tropicsquare/devboards/TROPIC01_Arduino_Shield/TS1401/doc/Arduino_UNO_R3_Pinout.jpg

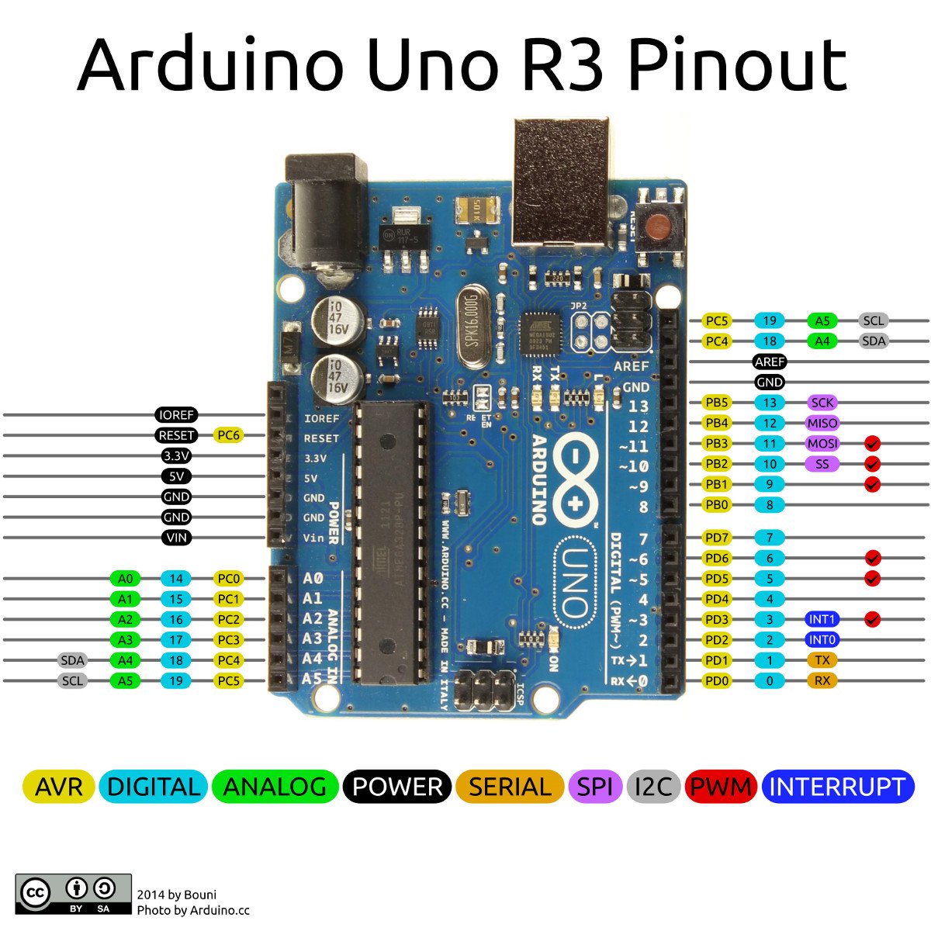
TROPIC01_Arduino_Shield/TS1401/doc/Arduino_UNO_R3_Pinout.jpg
