tropicsquare/devboards/TROPIC01_Arduino_Shield/TS1401/img/bot.png

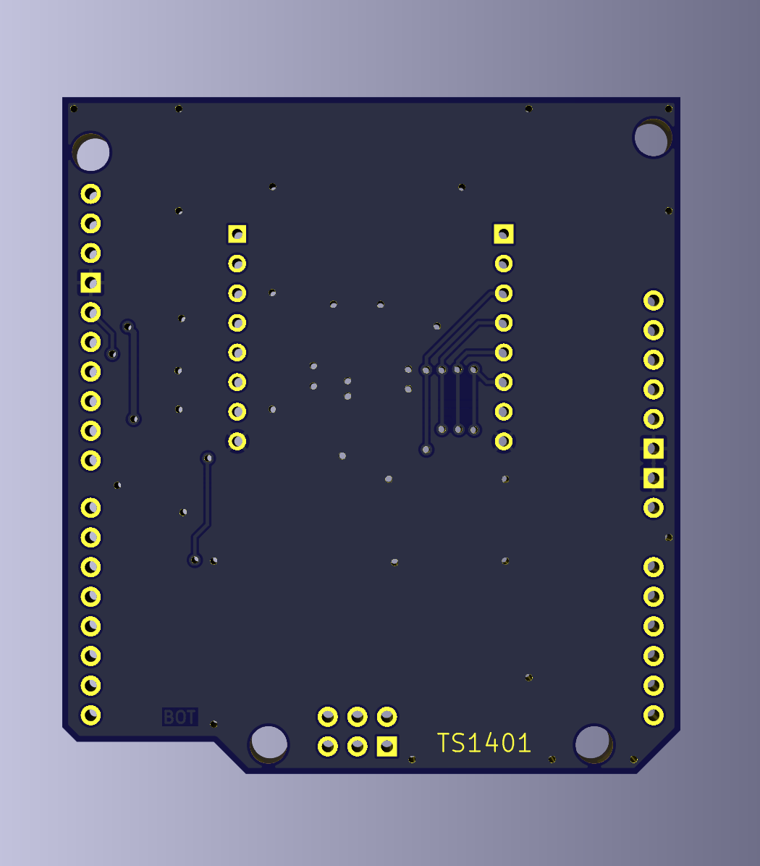
TROPIC01_Arduino_Shield/TS1401/img/bot.png
