tropicsquare/devboards/TROPIC01_Arduino_Shield/TS1401/img/top.png

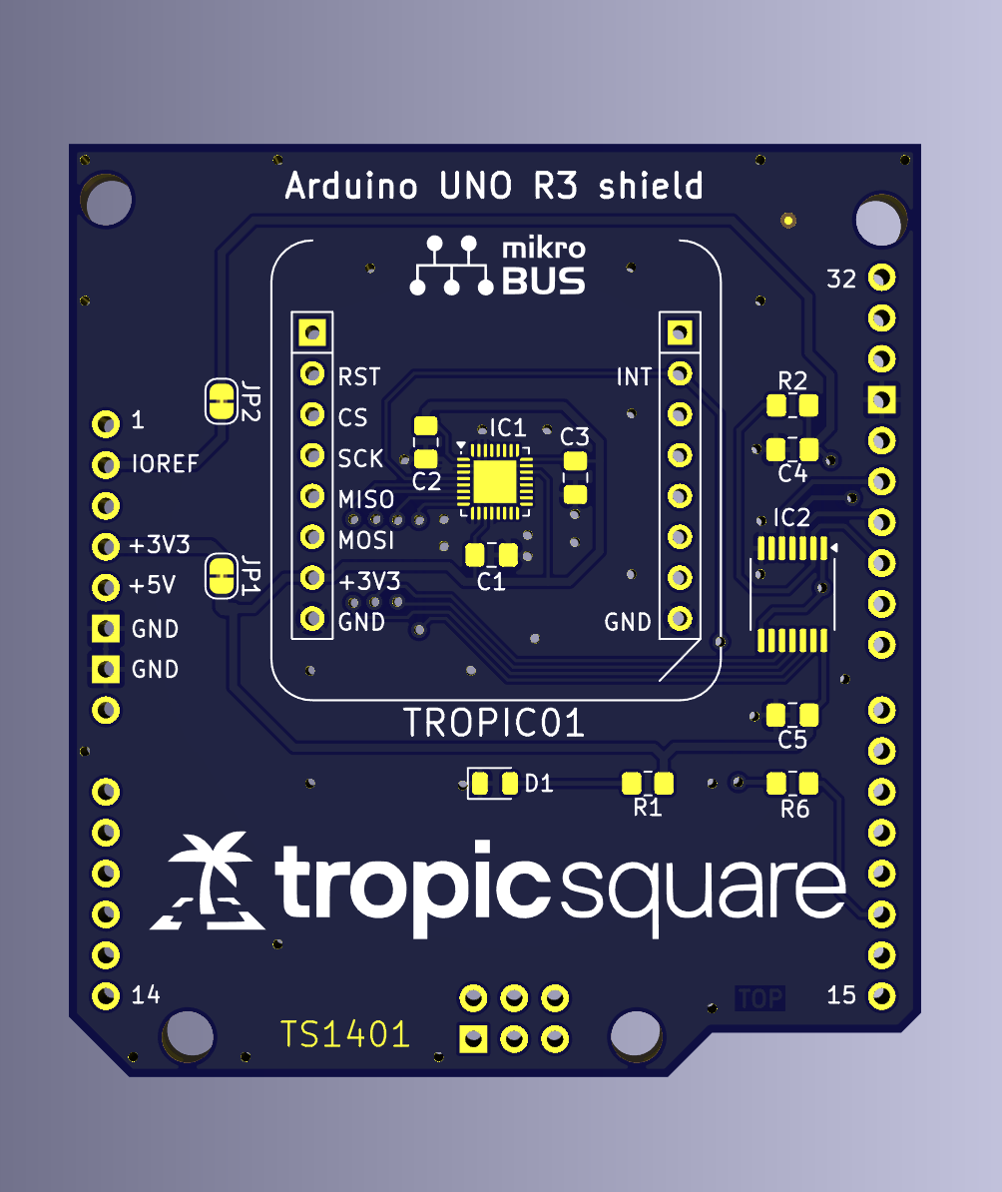
TROPIC01_Arduino_Shield/TS1401/img/top.png
