tropicsquare/devboards/TROPIC01_Mini_Board/TS1702/img/angle.png

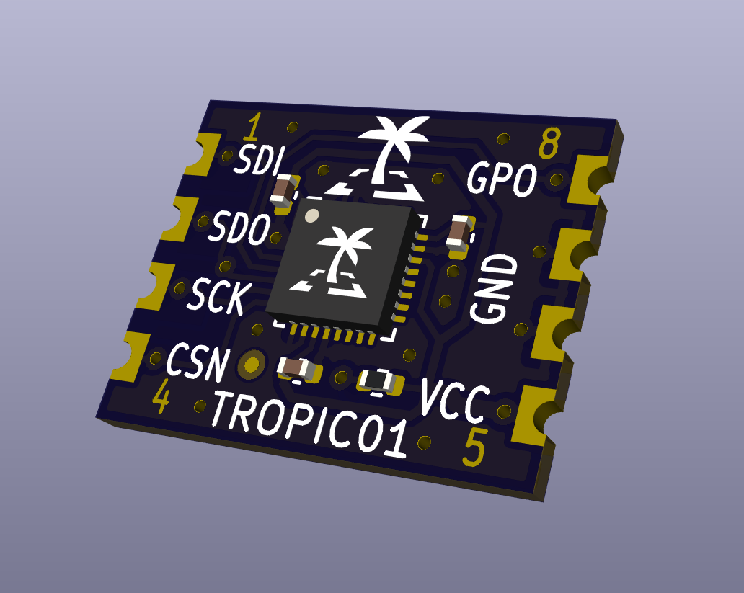
TROPIC01_Mini_Board/TS1702/img/angle.png
