tropicsquare/devboards/TROPIC01_Mini_Board/TS1702/img/bot.png

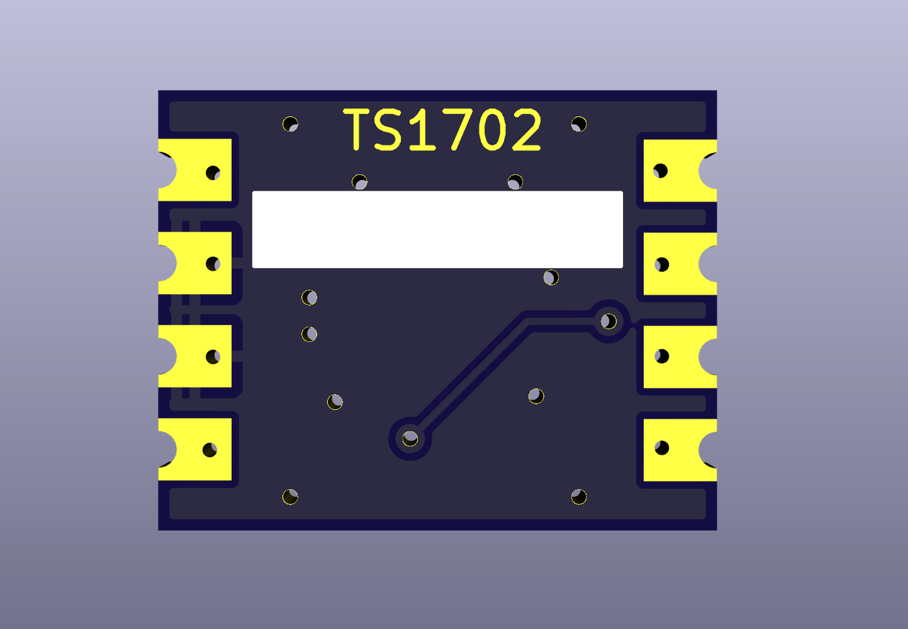
TROPIC01_Mini_Board/TS1702/img/bot.png
