tropicsquare/devboards/TROPIC01_Mini_Board/TS1702/img/dimensions.png

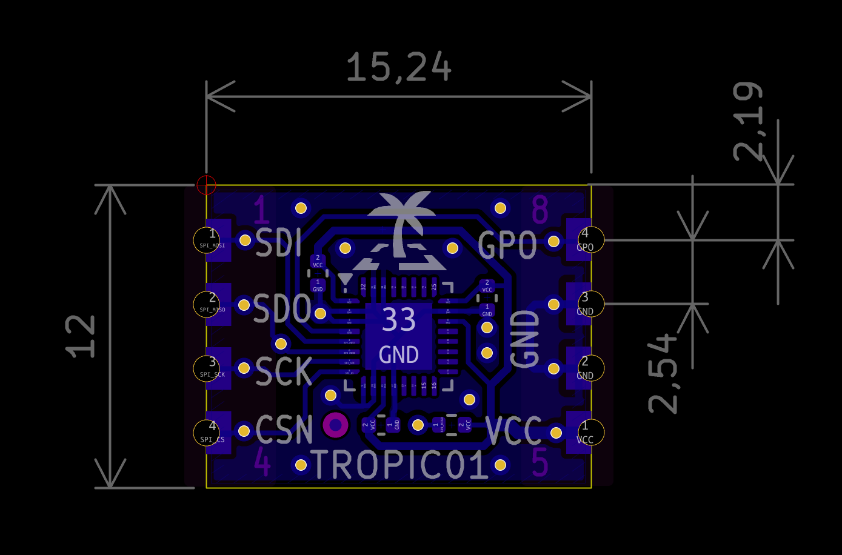
TROPIC01_Mini_Board/TS1702/img/dimensions.png
