tropicsquare/devboards/TROPIC01_Mini_Board/TS1702/img/overview.png

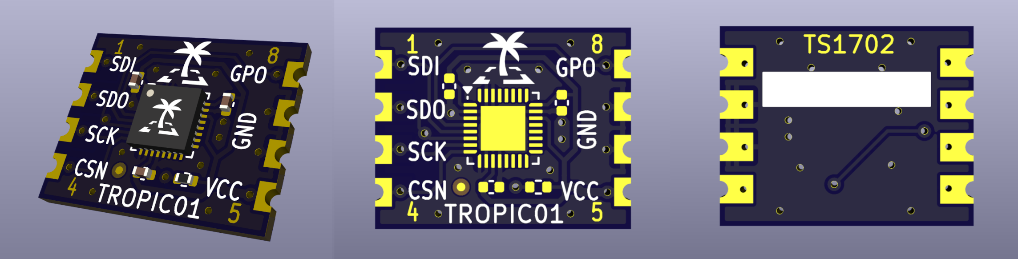
TROPIC01_Mini_Board/TS1702/img/overview.png
