tropicsquare/devboards/TROPIC01_Mini_Board/TS1702/img/top.png

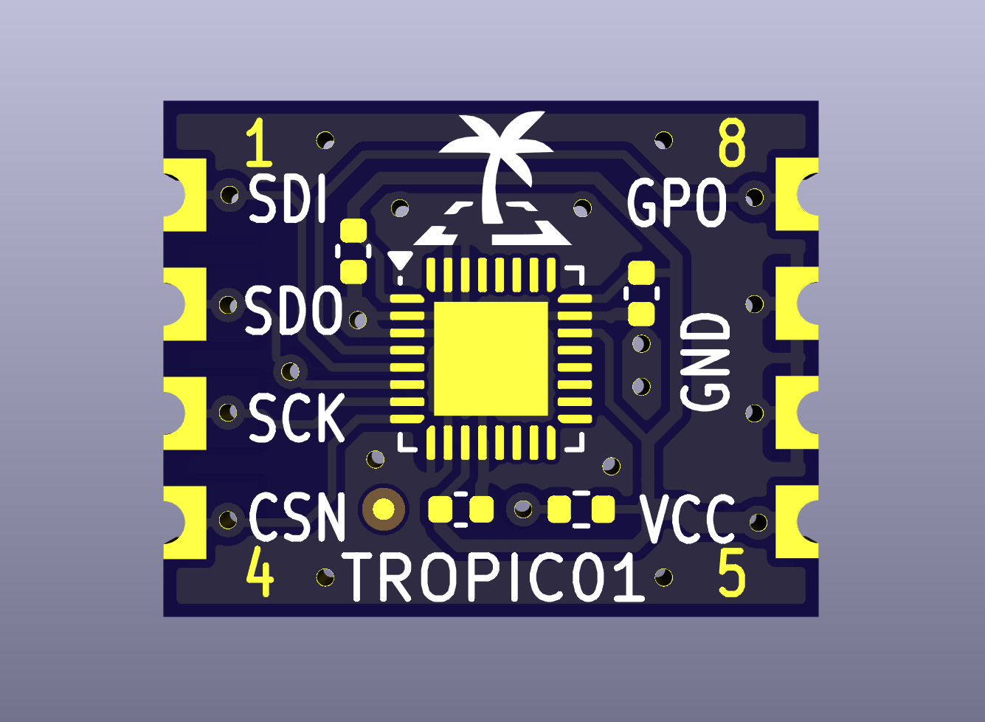
TROPIC01_Mini_Board/TS1702/img/top.png
