tropicsquare/devboards/TROPIC01_Raspberry_Pi_Shield/TS1501/img/top.png

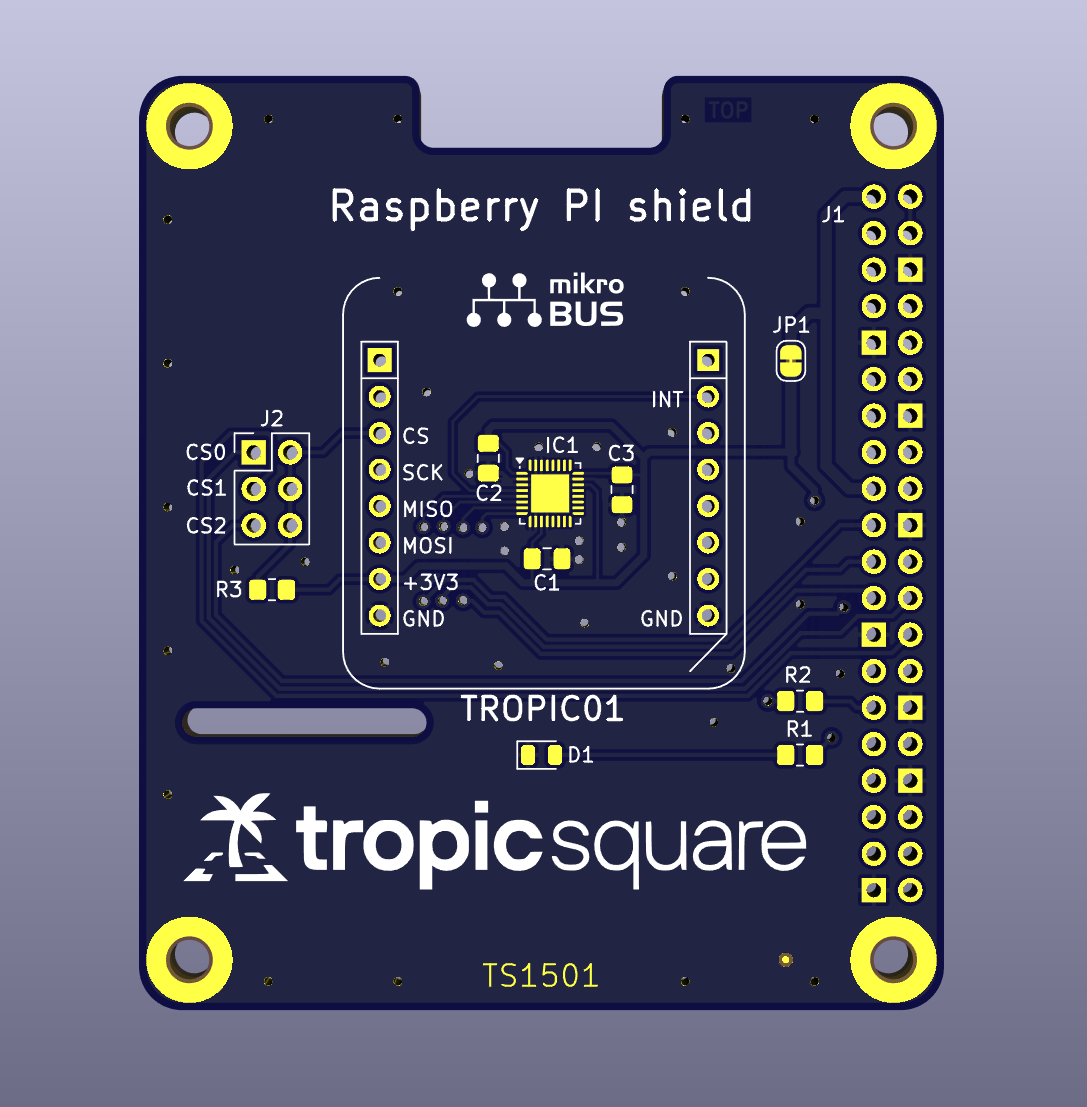
TROPIC01_Raspberry_Pi_Shield/TS1501/img/top.png
