tropicsquare/devboards/TROPIC01_USB_Devkit/firmwares/firmware_B/doc/ts1302_hw_bot.png

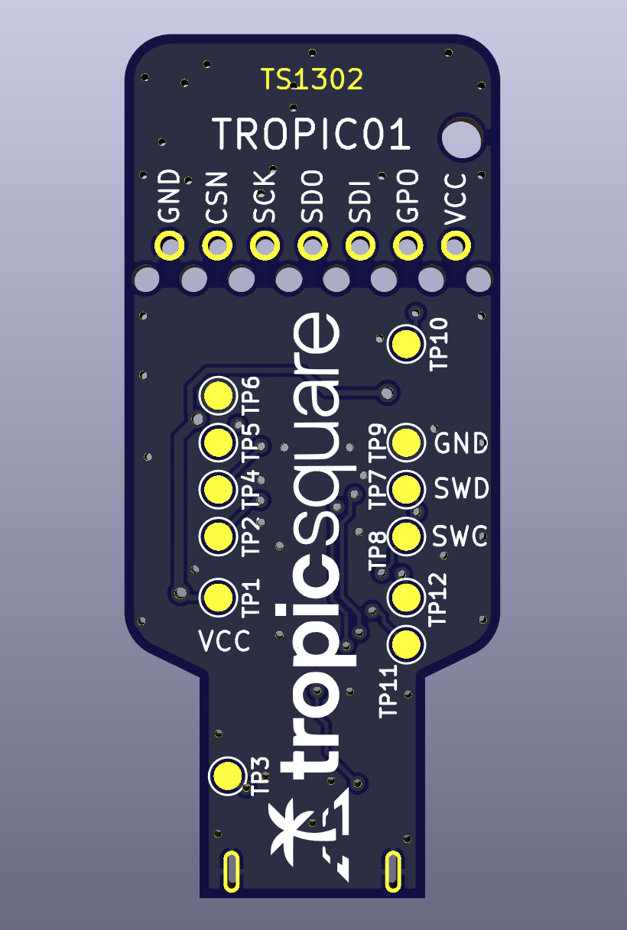
TROPIC01_USB_Devkit/firmwares/firmware_B/doc/ts1302_hw_bot.png
