tropicsquare/devboards/TROPIC01_USB_Devkit/firmwares/firmware_B/doc/ts1302_hw_top.png

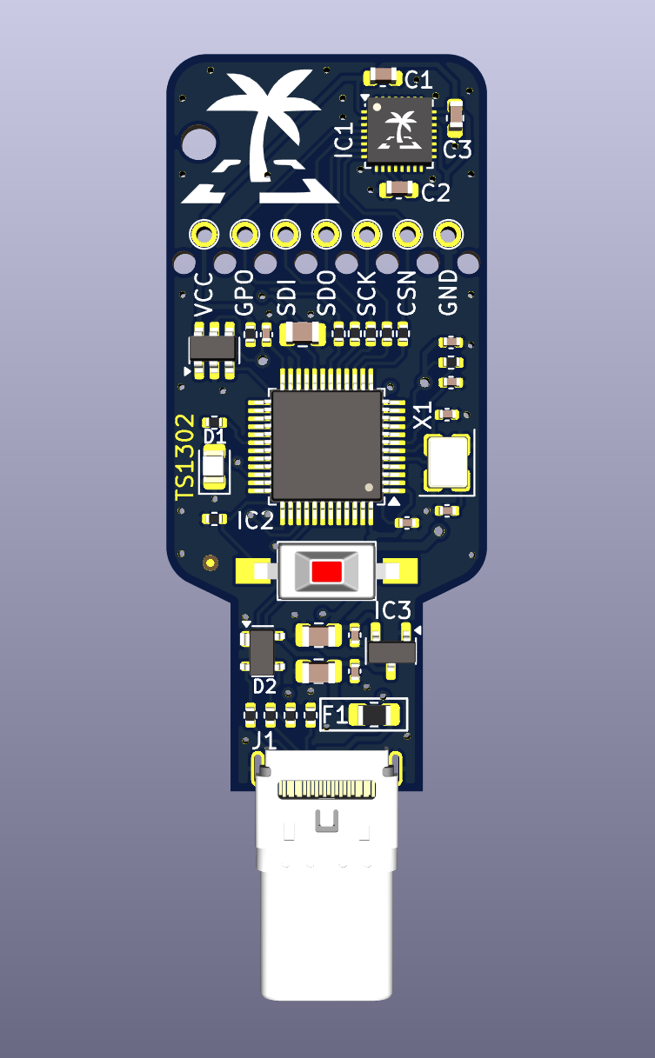
TROPIC01_USB_Devkit/firmwares/firmware_B/doc/ts1302_hw_top.png
