tropicsquare/devboards/TROPIC01_Arduino_Shield/TS1401/img/top_assembled.png

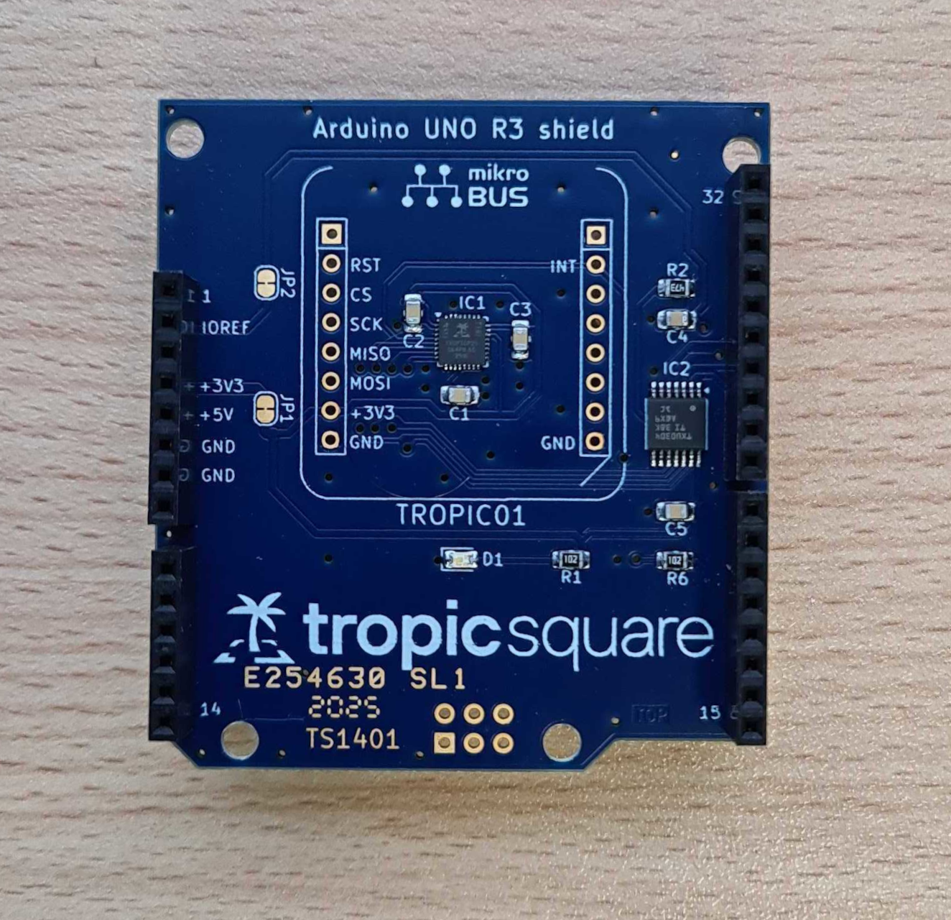
TROPIC01_Arduino_Shield/TS1401/img/top_assembled.png
