tropicsquare/devboards/TROPIC01_Raspberry_Pi_Shield/TS1501/img/bot_assembled.png

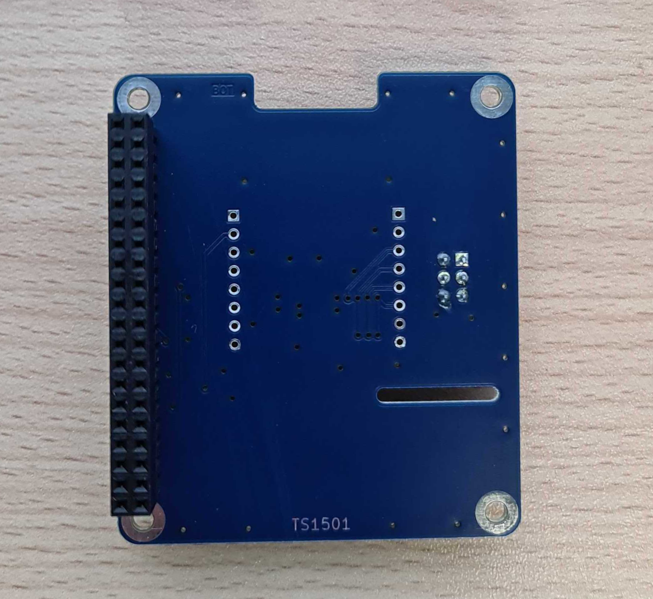
TROPIC01_Raspberry_Pi_Shield/TS1501/img/bot_assembled.png
